ImperialSpaceSociety/PicoTracker-MK-II/Spice/SX1276144M.asc

C1: cap; 47p
C2: cap; 47p
C3: cap; 27p
C4: cap; 4p7
C5: cap; 0p
L1: ind; 39n
L2: ind; 39n
L3: ind; 39n
R1: res; 50
R2: res; 50
V1: voltage; SINE(); AC 1
Named nets: 0
.ac dec 100 100Meg 1000Meg
SX1276 144MHz Low Pass Filter
