ImperialSpaceSociety/PicoTracker-MK-II/Spice/SX1276434M.asc

C1: cap; 15p
C2: cap; 12p
C3: cap; 4p7
C4: cap; 2p7
C5: cap; 0p
L1: ind; 12n
L2: ind; 18n
L3: ind; 22n
R1: res; 50
R2: res; 50
V1: voltage; SINE(); AC 1
Named nets: 0
.ac dec 100 100Meg 1000Meg
SX1276 434MHz Low Pass Filter
