ImperialSpaceSociety/PicoTracker-MK-II/Spice/SX1276868M.asc

C1: cap; 8p2
C2: cap; 3p3
C3: cap; 0p
C4: cap; 1p5
C5: cap; 0p
L1: ind; 4n7
L2: ind; 0n
L3: ind; 5n6
R1: res; 50
R2: res; 50
V1: voltage; SINE(); AC 1
Named nets: 0
.ac dec 100 100Meg 2000Meg
SX1276 434MHz Low Pass Filter
