ImperialSpaceSociety/PicoTracker-MK-II/prototype/firmware/EDBG UART erert/EDBG UART erert/driver_init.h

/*
 * Code generated from Atmel Start.
 *
 * This file will be overwritten when reconfiguring your Atmel Start project.
 * Please copy examples or other code you want to keep to a separate file
 * to avoid losing it when reconfiguring.
 */
#ifndef DRIVER_INIT_INCLUDED
#define DRIVER_INIT_INCLUDED

#include "atmel_start_pins.h"

#ifdef __cplusplus
extern "C" {
#endif

#include <hal_atomic.h>
#include <hal_delay.h>
#include <hal_gpio.h>
#include <hal_init.h>
#include <hal_io.h>
#include <hal_sleep.h>

#include <hal_usart_sync.h>

#include <hal_i2c_m_sync.h>

#include <hal_usart_sync.h>
#include <hal_spi_m_sync.h>

extern struct usart_sync_descriptor USART_0;

extern struct i2c_m_sync_desc I2C_0;

extern struct usart_sync_descriptor EDBG_COM_1;
extern struct spi_m_sync_descriptor SPI_0;

void USART_0_PORT_init(void);
void USART_0_CLOCK_init(void);
void USART_0_init(void);

void I2C_0_CLOCK_init(void);
void I2C_0_init(void);
void I2C_0_PORT_init(void);

void EDBG_COM_1_PORT_init(void);
void EDBG_COM_1_CLOCK_init(void);
void EDBG_COM_1_init(void);

void SPI_0_PORT_init(void);
void SPI_0_CLOCK_init(void);
void SPI_0_init(void);

/**
 * \brief Perform system initialization, initialize pins and clocks for
 * peripherals
 */
void system_init(void);

#ifdef __cplusplus
}
#endif
#endif // DRIVER_INIT_INCLUDED
